tangent3D/Z-FIGHTER/software/zf_lib/zf_hardware.c

// Hardware definitions for Z-Fighter
// Imported from <zf_hardware.h>
// by Tangent 2021

#include <zf_hardware.h>

__at (ROMDISABLE_n) void *romdisable_n;

__at (PORTA_ACC)    void *porta_acc;
__at (PORTB_ACC)    void *portb_acc;
__at (PORTC_ACC)    void *portc_acc;
__at (CTRL_ACC)     void *ctrl_acc;

__at (LCD_E_LO)     void *lcd_e_lo;
__at (LCD_E_HI)     void *lcd_e_hi;
__at (LCD_WR)       void *lcd_wr;
__at (LCD_RD)       void *lcd_rd;
__at (LCD_INST)     void *lcd_inst;
__at (LCD_DATA)     void *lcd_data;
__at (LCD_BL_OFF)   void *lcd_bl_off;
__at (LCD_BL_ON)    void *lcd_bl_on;
__at (BUZZER_OFF)   void *buzzer_off;
__at (BUZZER_ON)    void *buzzer_on;

__at (PORTA)        void *porta;
__at (PORTB)        void *portb;
__at (PORTC)        void *portc;
__at (CTRL)         void *ctrl;

__at (SIO)          void *sio;
__at (SIO_A)        void *sio_a;
__at (SIO_B)        void *sio_b;
__at (SIO_AC)       void *sio_ac;
__at (SIO_BC)       void *sio_bc;

__at (CF0)          void *cf0;
__at (CF1)          void *cf1;
__at (CF2)          void *cf2;
__at (CF3)          void *cf3;
__at (CF4)          void *cf4;
__at (CF5)          void *cf5;
__at (CF6)          void *cf6;
__at (CF7)          void *cf7;
