tangent3D/Z-FIGHTER/software/zf_lib/zf_text.c

// Bitmap text implementation for Z-Fighter
// by Tangent 2021

#include <zf_text.h>
#include <zf_gfx.h>

void print(unsigned char string[], unsigned char x, unsigned char y)
{
    unsigned char i = 0;
    while (string[i] != '\0')
    {
        if(string[i] == '\n')
        {
            x = 0;
            y++;
            i++;
        }
        unsigned char j = string[i]-32;
        block(charSet+(j<<3), x, y);
        x++;
        i++;
    }
}

void printChar(unsigned char character, unsigned char x, unsigned char y)
{
    block(charSet+(character-32)*8, x, y);
}

const unsigned char charSet [] =
{
    0x00, 0x00, 0x00, 0x00, 0x00, 0x00, 0x00, 0x00, 0x00, 0x10, 0x10, 0x10, 0x10, 0x00, 0x10, 0x00,
    0x00, 0x24, 0x24, 0x00, 0x00, 0x00, 0x00, 0x00, 0x00, 0x24, 0x7E, 0x24, 0x24, 0x7E, 0x24, 0x00,
    0x10, 0x3C, 0x40, 0x38, 0x04, 0x78, 0x10, 0x00, 0x00, 0x62, 0x64, 0x08, 0x10, 0x26, 0x46, 0x00,
    0x10, 0x28, 0x10, 0x2A, 0x44, 0x44, 0x3A, 0x00, 0x00, 0x10, 0x10, 0x20, 0x00, 0x00, 0x00, 0x00,
    0x08, 0x10, 0x10, 0x10, 0x10, 0x10, 0x08, 0x00, 0x10, 0x08, 0x08, 0x08, 0x08, 0x08, 0x10, 0x00,
    0x00, 0x54, 0x38, 0x7C, 0x38, 0x54, 0x00, 0x00, 0x00, 0x10, 0x10, 0x7C, 0x10, 0x10, 0x00, 0x00,
    0x00, 0x00, 0x00, 0x00, 0x10, 0x10, 0x20, 0x00, 0x00, 0x00, 0x00, 0x3C, 0x00, 0x00, 0x00, 0x00,
    0x00, 0x00, 0x00, 0x00, 0x00, 0x30, 0x30, 0x00, 0x00, 0x02, 0x04, 0x08, 0x10, 0x20, 0x40, 0x00,
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
    0x00, 0x10, 0x10, 0x10, 0x10, 0x10, 0x08, 0x00, 0x00, 0x00, 0x68, 0x54, 0x54, 0x44, 0x44, 0x00,
    0x00, 0x00, 0x78, 0x44, 0x44, 0x44, 0x44, 0x00, 0x00, 0x00, 0x38, 0x44, 0x44, 0x44, 0x38, 0x00,
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
};
