tangent3D/Z-FIGHTER/software/zf_lib/zf_ppi.c

// 8255A Programmable Peripheral Interface implementation for Z-Fighter
// (User parallel port)
// by Tangent 2021

#include <zf_ppi.h>

unsigned char bitOrder = MSB;

unsigned char serialRead(unsigned char dataPin, unsigned char clockPin)
{
    unsigned char byte = 0;

    for(unsigned char i = 0; i < 8; i++)                        // Repeat 8 times
    {
        ctrl = clockPin+1;                                      // Pulse specified clock pin
        ctrl = clockPin+0;

        byte = byte | bitTest(dataPin >> 1, pc);                // Assemble a byte by reading serially from specified data pin on port C

        if(i != 7)
        {
            byte = byte << 1;
        }
    }

    if(bitOrder == LSB)                                         // Reverse byte's bit order if reading LSB first
    {
        byte = byteReverse(byte);
    }

    return(byte);
}

void serialWrite(unsigned char byte, unsigned char dataPin, unsigned char clockPin)
{
    unsigned char bit = 0;

    if(bitOrder == MSB)                                         // Reverse byte's bit order if writing LSB first
    {
        byte = byteReverse(byte);
    }

    for(unsigned char i = 0; i < 8; i++)                        // Repeat 8 times
    {
        ctrl = dataPin + bitTest(bit, byte);                    // Set specified data pin high or low according to its position in byte
        ctrl = clockPin+1;                                      // Pulse specified clock pin
        ctrl = clockPin+0;
        bit++;
    }
}


unsigned char bitTest(unsigned char bit, unsigned char byte)
{
    unsigned char bitMask = 0x01 << bit;
    byte = bitMask & byte;
    return(byte >> bit);
}

unsigned char bcd2bin(unsigned char bcd)
{
    unsigned char hiNibble = bcd >> 4;
    unsigned char loNibble = bcd & 0x0F;
    return((hiNibble * 10) + loNibble);
}

unsigned char bin2bcd(unsigned char bin)
{
    unsigned char tens = 0;
    unsigned char ones = 0;

    for(unsigned char i = 0; i < 8; i++)
    {
        if(tens >= 5)
        {
            tens = tens + 3;
        }
        if(ones >= 5)
        {
            ones = ones + 3;
        }

        tens = tens << 1;
        tens = tens + (ones >> 3);

        ones = ones << 1;
        ones = ones + (bin >> 7);
        ones = ones & 0x0F;

        bin = bin << 1;
    }
    unsigned char bcd = (tens << 4) | ones;
    return(bcd);
}
