tangent3D/Z-FIGHTER/software/zf_lib/zf_text.h

// Bitmap text definitions for Z-Fighter
// by Tangent 2021

#ifndef ZF_TEXT_H
#define ZF_TEXT_H

void print(unsigned char string[], unsigned char x, unsigned char y);

void printChar(unsigned char character, unsigned char x, unsigned char y);

extern const unsigned char charSet[];

#endif
